hervestudio/speaker-badges/speaker_badge_long.step

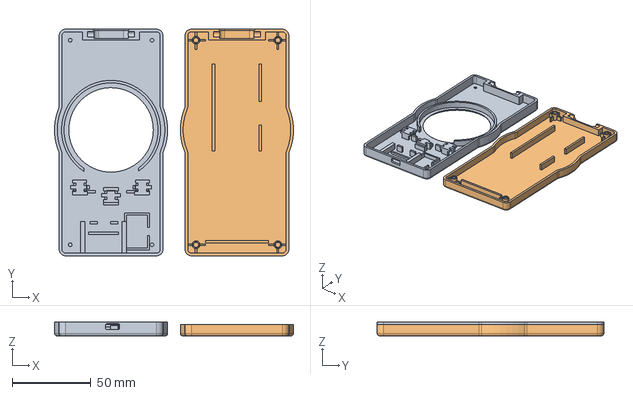
[picture p15: CAD file, 2026-08-17]
speaker_badge_long.step
151.9 x 144.0 x 8.75 mm
front_shell
back_shell
