hervestudio/speaker-badges/compare_buttons.step

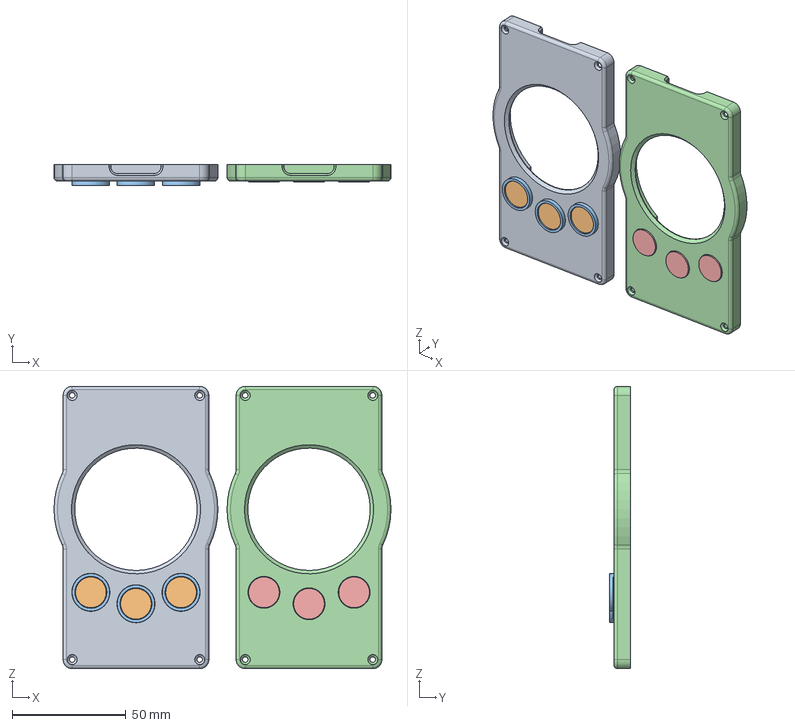
[picture p16: CAD file, 2026-08-03]
compare_buttons.step
148.0 x 9.25 x 124.0 mm
front_ring
cap_ring_0
ring_ring_0
cap_ring_1
ring_ring_1
cap_ring_2
ring_ring_2
front_flush
cap_flush_0
cap_flush_1
cap_flush_2
