hervestudio/speaker-badges/print/buttons_smiley_15.gcode.3mf

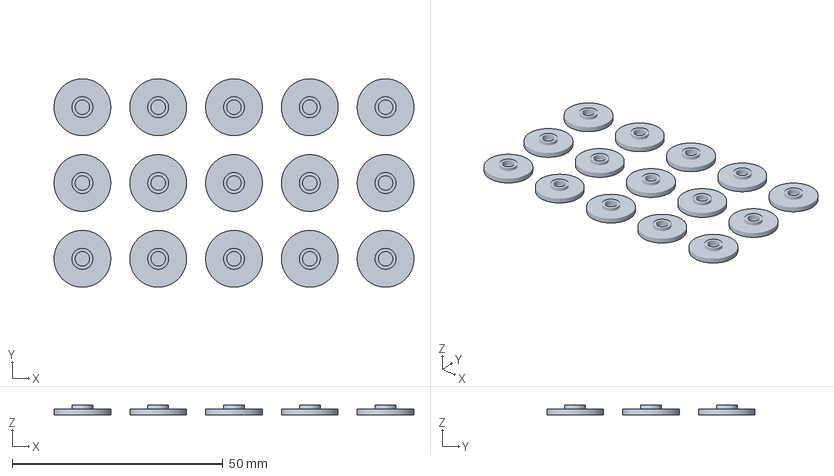
[picture p17: CAD file, 2026-08-27]
print/buttons_smiley_15.gcode.3mf
85.5 x 49.5 x 2.30 mm
