hervestudio/speaker-badges/exploded_view.step

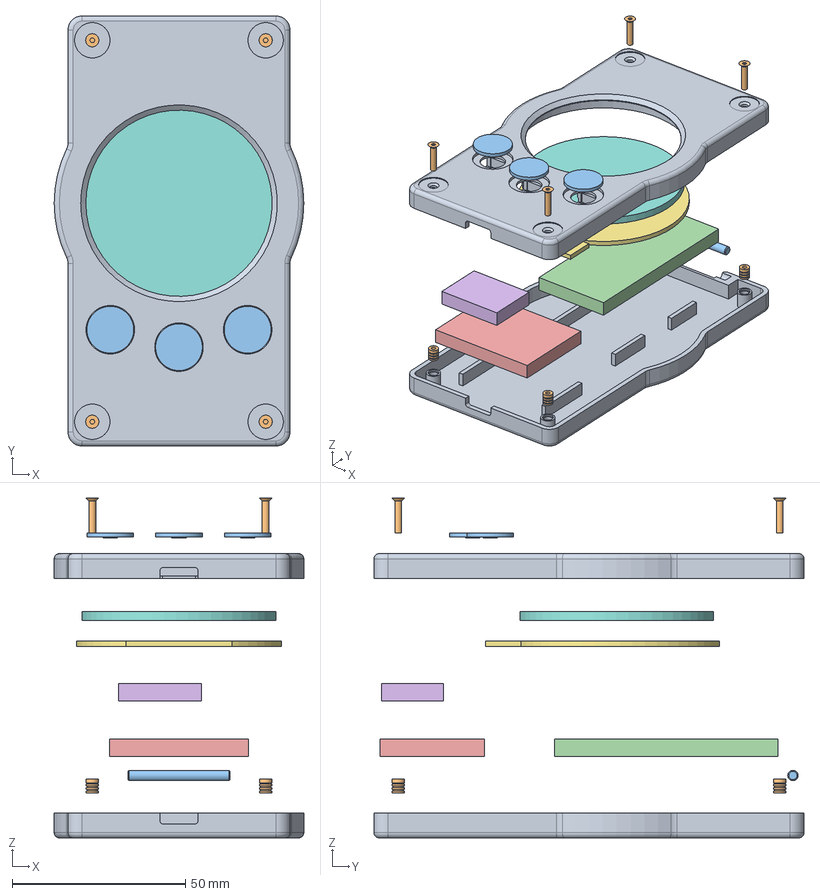
[picture p18: CAD file, 2026-08-03]
exploded_view.step
72.0 x 124.0 x 98.0 mm
back_shell
insert_3 x 4
wrap_bar
esp32_s3
lipo_503040
tp4056_boost
tft_pcb
tft_glass
front_shell
screw_3 x 4
button_cap_center
button_cap_1
button_cap_2
