hervestudio/speaker-badges/section_view.step

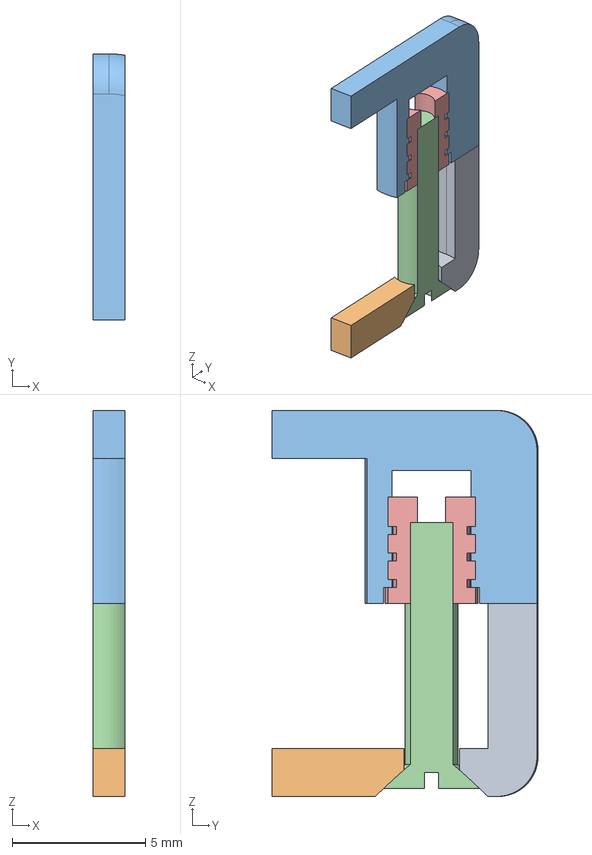
[picture p19: CAD file, 2026-08-03]
section_view.step
1.20 x 10.0 x 14.5 mm
front_shell
back_shell
screw_3
insert_3
