hervestudio/speaker-badges/badge_v2.step

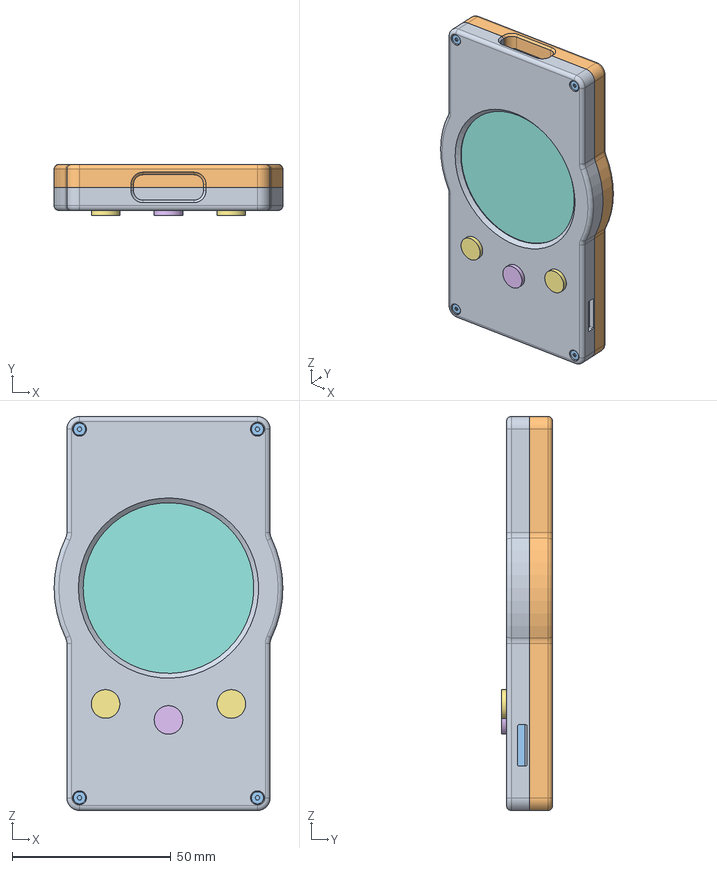
[picture p20: CAD file, 2026-07-30]
badge_v2.step
72.0 x 16.1 x 124.0 mm
front_shell
back_shell
screw_3 x 4
insert_3 x 4
wrap_bar
button_cap_center
button_cap_1
button_cap_2
tft_glass
tft_pcb
tp4056_boost
sd_module
esp32_s3
lipo_503040
