hervestudio/speaker-badges/compare_v1_v2.step

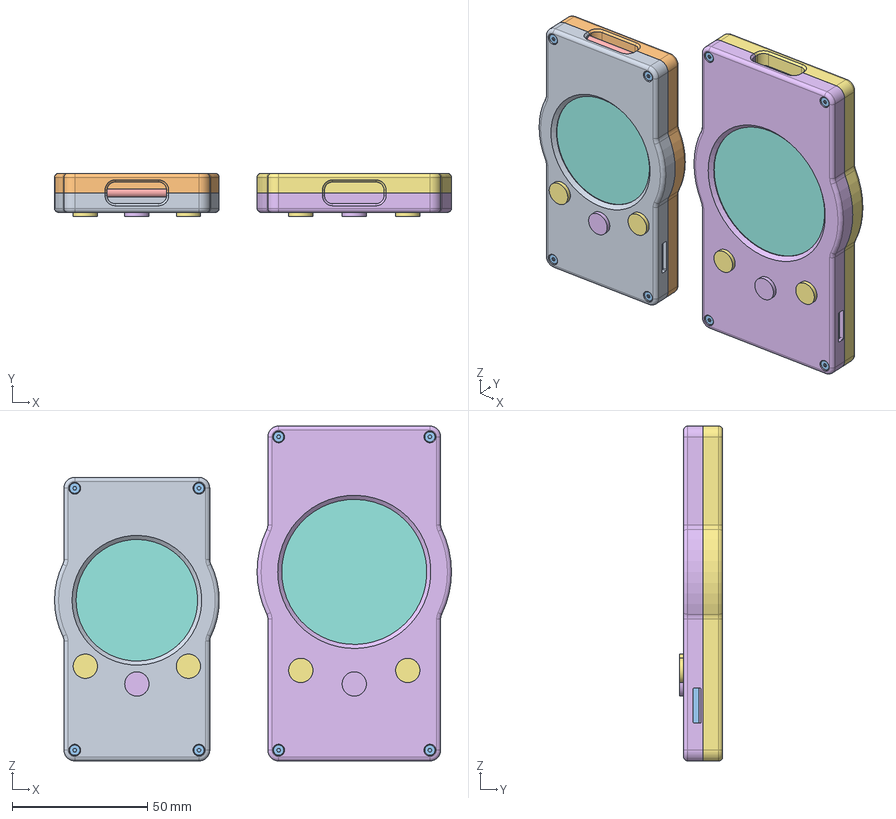
[picture p21: CAD file, 2026-07-30]
compare_v1_v2.step
147.0 x 16.1 x 124.0 mm
front_shell x 2
back_shell x 2
screw_3 x 8
insert_3 x 8
wrap_bar x 2
button_cap_center x 2
button_cap_1 x 2
button_cap_2 x 2
amoled_glass
screen_adapter
tp4056_boost x 2
sd_module x 2
esp32_s3 x 2
lipo_503040 x 2
tft_glass
tft_pcb
