hervestudio/speaker-badges/print/buttons_inlay_test.gcode.3mf

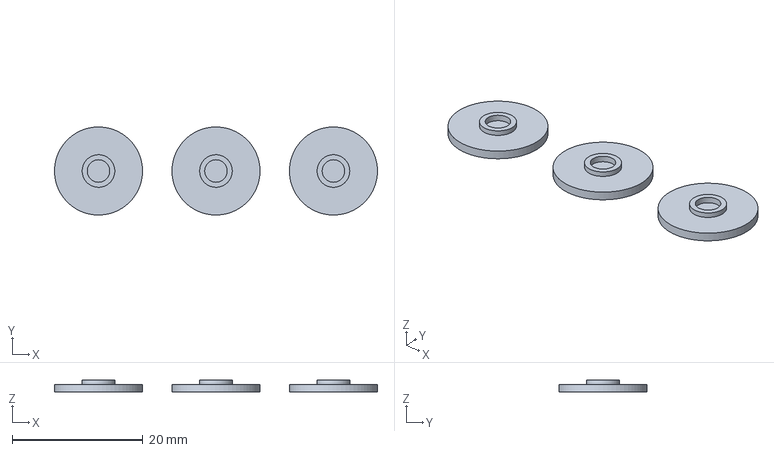
[picture p22: CAD file, 2026-08-26]
print/buttons_inlay_test.gcode.3mf
49.5 x 13.5 x 1.90 mm
