hervestudio/speaker-badges/print/back_shell_short.stl

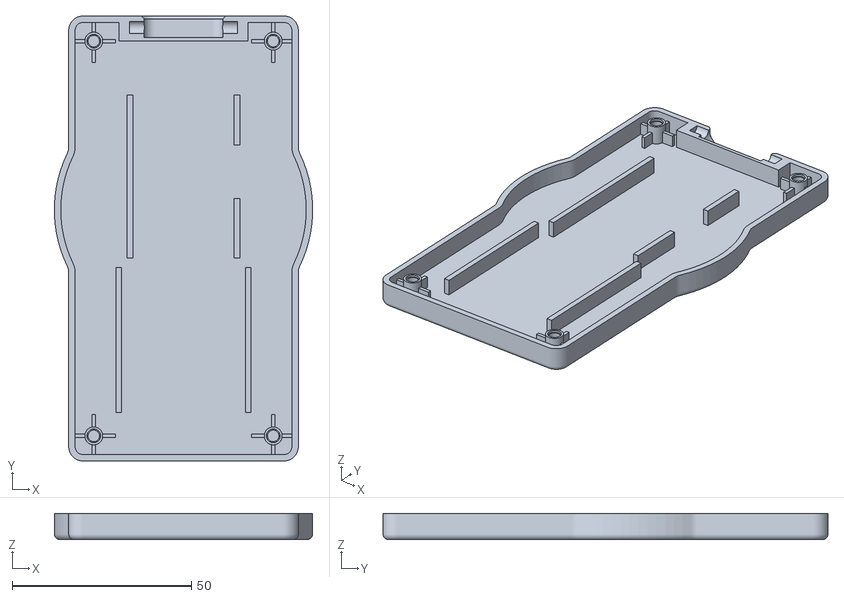
[picture p23: CAD file, 2026-08-17]
print/back_shell_short.stl
72.0 x 124.0 x 7.25
