hervestudio/speaker-badges/print/back_shell_long.stl

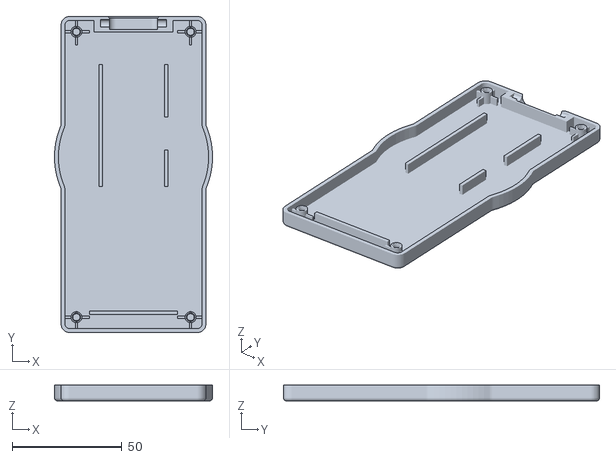
[picture p25: CAD file, 2026-08-17]
print/back_shell_long.stl
72.0 x 144.0 x 7.25
