hervestudio/speaker-badges/print/button_cap_side_inlay.stl

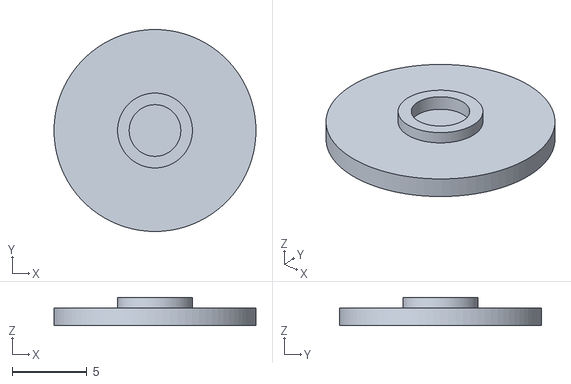
[picture p26: CAD file, 2026-08-17]
print/button_cap_side_inlay.stl
13.5 x 13.5 x 1.90
