hervestudio/speaker-badges/print/front_shell_short.stl

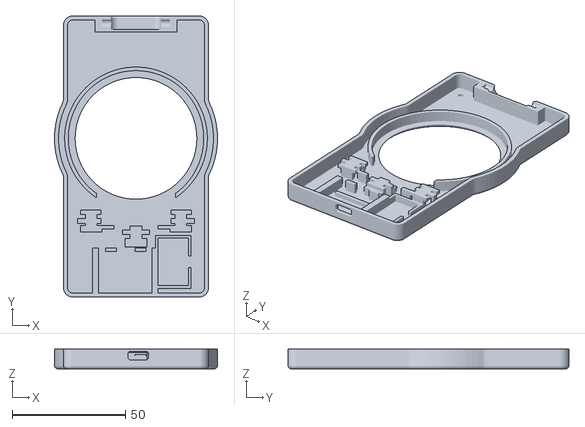
[picture p27: CAD file, 2026-08-17]
print/front_shell_short.stl
72.0 x 124.0 x 8.75
