hervestudio/speaker-badges/print/front_shell_long.stl

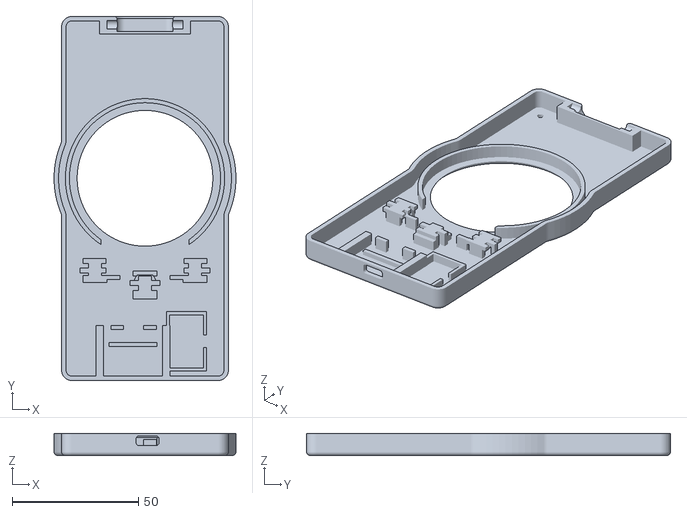
[picture p28: CAD file, 2026-08-17]
print/front_shell_long.stl
72.0 x 144.0 x 8.75
