hervestudio/speaker-badges/print/back_shell_medium.stl

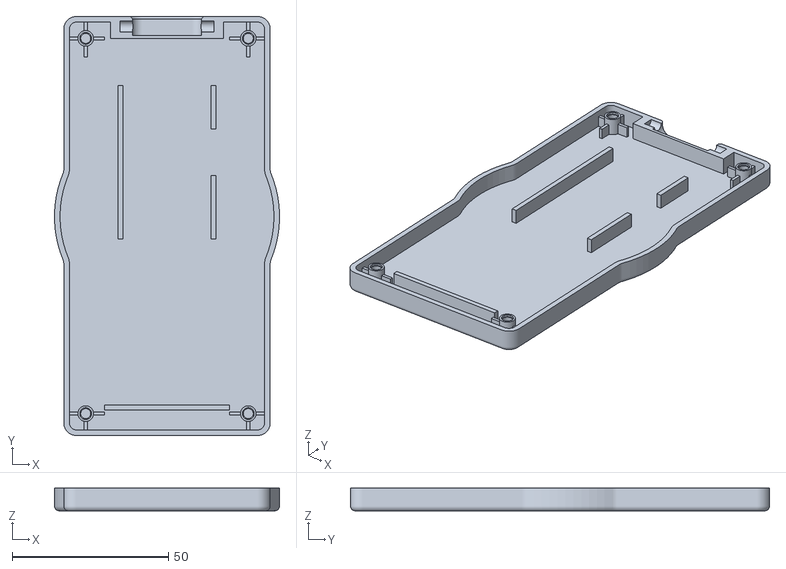
[picture p29: CAD file, 2026-08-17]
print/back_shell_medium.stl
72.0 x 134.0 x 7.25
