hervestudio/speaker-badges/print/button_cap_center_dome.stl

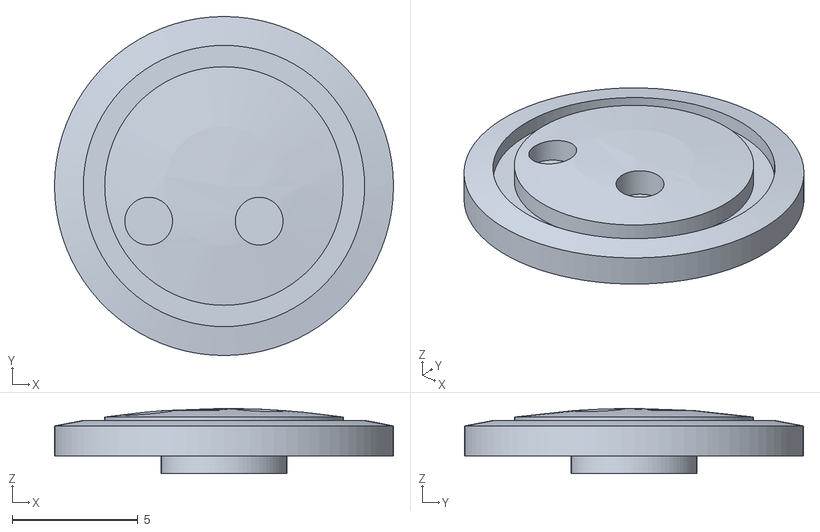
[picture p31: CAD file, 2026-08-17]
print/button_cap_center_dome.stl
13.5 x 13.5 x 2.60
